pilotak/WemosWeatherStation/code/WemosWeatherStation/mqtt.h

void sendStatus() {
    if (mqtt.connected()) {
        StaticJsonDocument < JSON_OBJECT_SIZE(6) > json;
        char message[140];

        json["status"] = MQTT_STATUS_ALIVE;
        json["ip"] = WiFi.localIP().toString();
        json["signal"] = wifiManager.getRSSIasQuality(WiFi.RSSI());
        json["sensors"] = sensor_state;
        json["fw_ver"] = FW_VERSION;

        uint32_t len = serializeJson(json, message, sizeof(message));

#if defined(DEBUG)
        Serial.println("[MQTT] Sending status data:");
        serializeJsonPretty(json, Serial);
        Serial.println();
#endif

        mqtt.publish(MQTT_STATUS_TOPIC, MQTT_QOS, MQTT_RETAIN, message, len);
    }
}

void onMqttMessage(char* topic, char* payload, AsyncMqttClientMessageProperties properties, size_t len, size_t index, size_t total) {
#if defined(DEBUG)
    Serial.print("[MQTT] Message arrived [");
    Serial.print(topic);
    Serial.print("]: ");

    for (uint16_t i = 0; i < len; i++) {
        Serial.print(static_cast<char>(payload[i]));
    }

    Serial.println();
#endif

    if (strcmp(topic, MQTT_HEIGHT_UPDATE_TOPIC) == 0 && len > 0) {
#if defined(HAS_BARO)

        if (atoi(payload) > 0) {
            height_above_sea = atoi(payload);
            saveConfig();

            // confirm
            mqtt.publish(MQTT_HEIGHT_NEW_TOPIC, MQTT_QOS, false, payload, len);
        }

#endif

    } else if (strcmp(topic, MQTT_UPGRADE_TOPIC) == 0 && len >= 4) {
#if defined(HTTP_OTA)

        if (len > sizeof(http_ota_url)) {
            mqtt.publish(MQTT_UPGRADE_STATUS_TOPIC, MQTT_QOS, false, "URL too long");

        } else {
            memset(http_ota_url, 0, sizeof(http_ota_url));
            memcpy(http_ota_url, payload, len);
            do_http_update = true;
        }

#endif

    } else if (strcmp(topic, MQTT_RESTART_TOPIC) == 0) {
        wifiManager.reboot();
    }
}

void connectToMqtt() {
#if defined(DEBUG)
    Serial.print("[MQTT] Connecting to: ");
    Serial.print(mqtt_server);
    Serial.print(":");
    Serial.println(mqtt_port);
#endif

    mqtt.connect();
}

void onMqttConnect(bool sessionPresent) {
#if defined(DEBUG)
    Serial.println("[MQTT] Connected");
#endif

    mqtt.subscribe(MQTT_RESTART_TOPIC, MQTT_QOS);

#if defined(SENSOR_BMP280)
    mqtt.subscribe(MQTT_HEIGHT_UPDATE_TOPIC, MQTT_QOS);
#endif

#if defined(HTTP_OTA)
    mqtt.subscribe(MQTT_UPGRADE_TOPIC, MQTT_QOS);
#endif

    sendStatus();
}

void onMqttDisconnect(AsyncMqttClientDisconnectReason reason) {
    if (!ota_in_progess) {
#if defined(DEBUG)

        if ((int8_t)reason != 0) {
            Serial.print("[MQTT] Disconnected, rc=");
            Serial.println((int8_t)reason);
        }

#endif

        if (WiFi.isConnected()) {
            mqttReconnectTimer.once(2, connectToMqtt);
        }
    }
}

void mqttSetup() {
#if defined(DEBUG)
    Serial.println("[MQTT] Setup");
#endif

    IPAddress ip;

    if (ip.fromString(mqtt_server)) {  // check if server is IP address or hostname
        mqtt.setServer(ip, mqtt_port);

    } else {
        mqtt.setServer(mqtt_server, mqtt_port);
    }

    snprintf(will, sizeof(will), "{\"status\": %i}", MQTT_STATUS_DEAD);

    mqtt.setCredentials(mqtt_user, mqtt_password);
    mqtt.setWill(MQTT_STATUS_TOPIC, MQTT_QOS, MQTT_RETAIN, will, strlen(will));
    mqtt.setKeepAlive((MQTT_STATUS_INTERVAL / 1000) + 2);  // converts ms->s + 2 sec extra, in case we have a delay
    mqtt.onConnect(onMqttConnect);
    mqtt.onDisconnect(onMqttDisconnect);
    mqtt.onMessage(onMqttMessage);
}

void mqttLoop() {
    static uint32_t last_status = 0;

    if (!ota_in_progess) {
        if ((millis() - last_status) >= MQTT_STATUS_INTERVAL) {
            last_status = millis();

            sendStatus();
        }
    }
}
